Bored-guy-with-ADHD/Mesh-IT/Assests/enclosure_photo.png

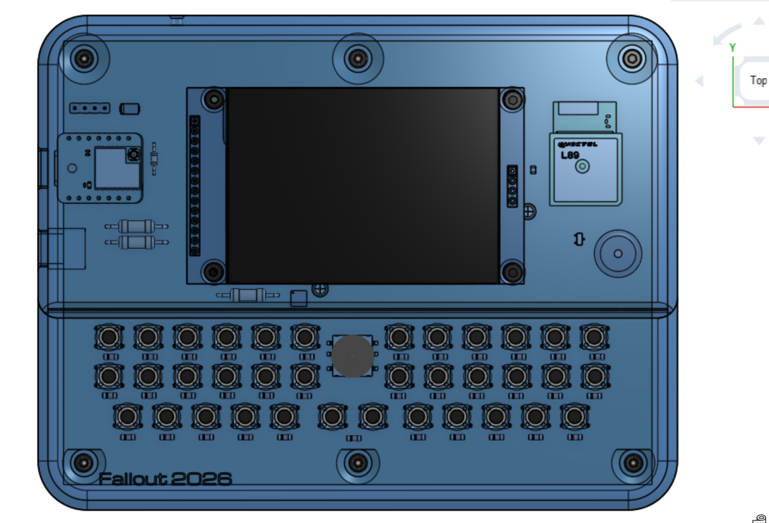
Assests/enclosure_photo.png
