Bored-guy-with-ADHD/Mesh-IT/Assests/pcb_photo.png

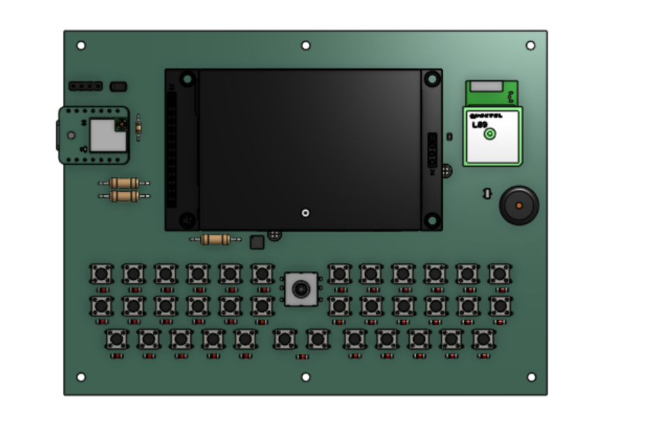
Assests/pcb_photo.png
