Bored-guy-with-ADHD/Mesh-IT/Assests/pcb_photo_rtx.png

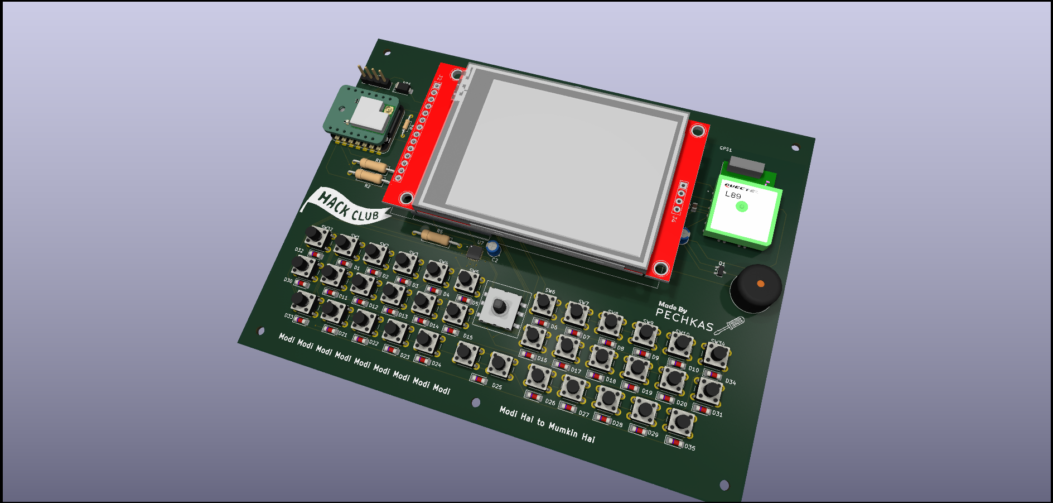
Assests/pcb_photo_rtx.png
